robertsmatt97/educational-resonant-demo/KiCAD/Resonant_Edit/Footprints/LLL31MR71C105MA01L.stp

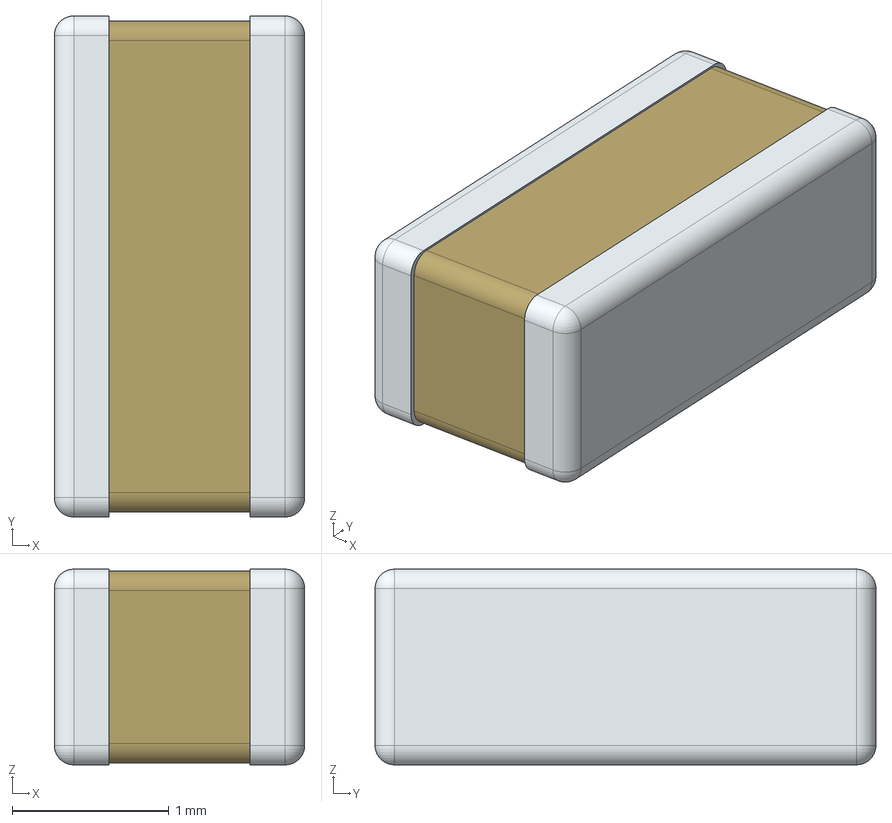
[picture p1: CAD file, 2020-12-04]
KiCAD/Resonant_Edit/Footprints/LLL31MR71C105MA01L.stp
1.60 x 3.20 x 1.25 mm
