robertsmatt97/educational-resonant-demo/KiCAD/Resonant_Edit/Parts/PMEG2010AEH,115.stp

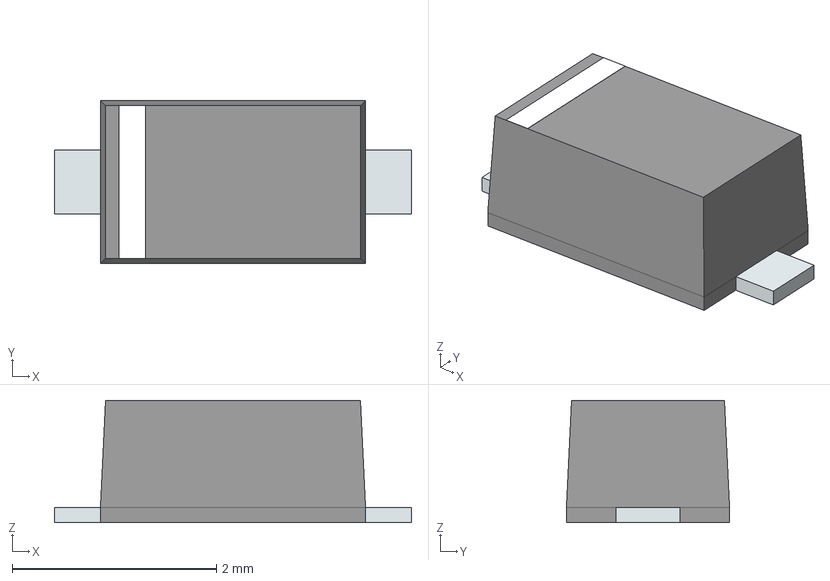
[picture p2: CAD file, 2020-12-04]
KiCAD/Resonant_Edit/Parts/PMEG2010AEH,115.stp
3.50 x 1.60 x 1.20 mm
PinKIdent
PinK
PinA
