robertsmatt97/educational-resonant-demo/KiCAD/Resonant_Edit/Footprints/PTV09A-4020U-B103.stp

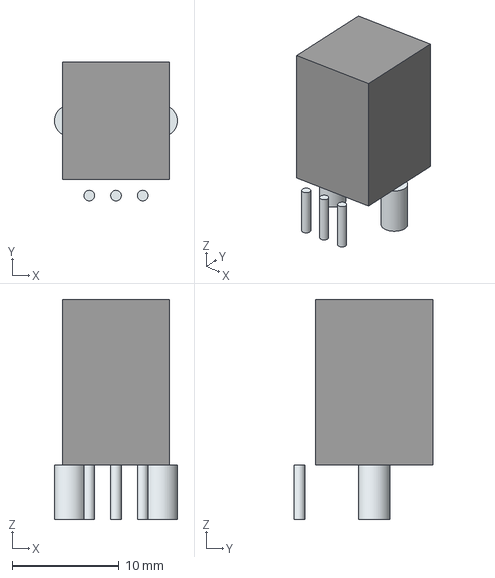
[picture p3: CAD file, 2020-12-04]
KiCAD/Resonant_Edit/Footprints/PTV09A-4020U-B103.stp
11.5 x 13.0 x 20.6 mm
Leads x 5
