robertsmatt97/educational-resonant-demo/KiCAD/Resonant_Edit/Footprints/VSSC8L45-M3_9AT.stp

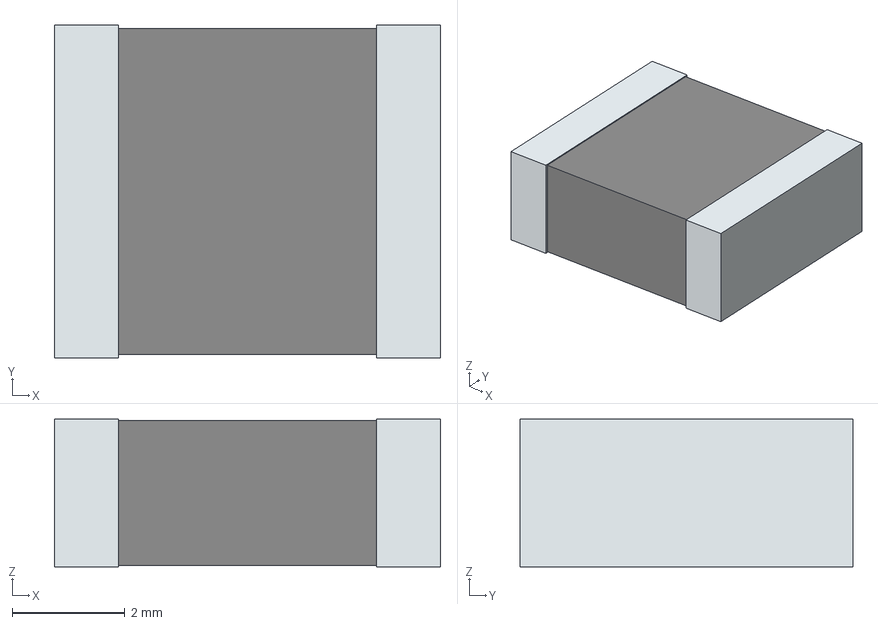
[picture p4: CAD file, 2020-12-04]
KiCAD/Resonant_Edit/Footprints/VSSC8L45-M3_9AT.stp
6.86 x 5.91 x 2.62 mm
term1
term2
