robertsmatt97/educational-resonant-demo/KiCAD/Resonant_Edit/Parts/MBR1H100SFT3G.stp

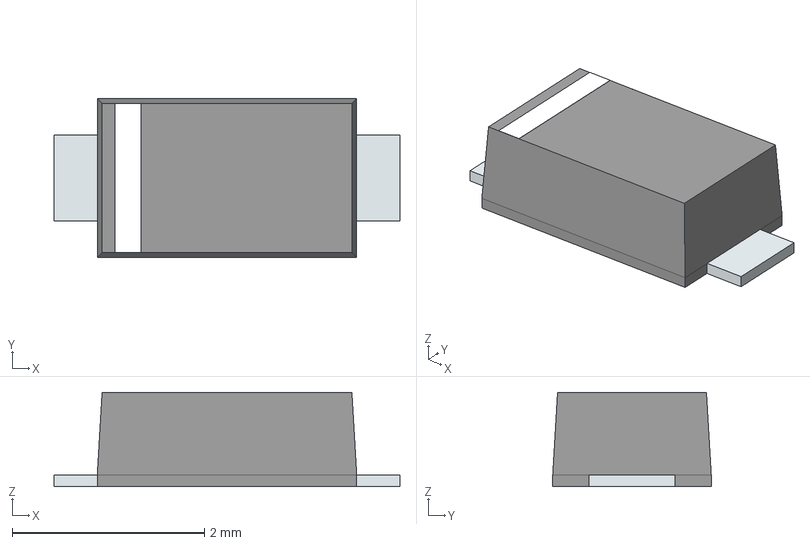
[picture p5: CAD file, 2020-12-04]
KiCAD/Resonant_Edit/Parts/MBR1H100SFT3G.stp
3.60 x 1.65 x 0.98 mm
PinKIdent
PinK
PinA
