robertsmatt97/educational-resonant-demo/KiCAD/Resonant_Edit/Footprints/LM5109BSD_NOPB.stp

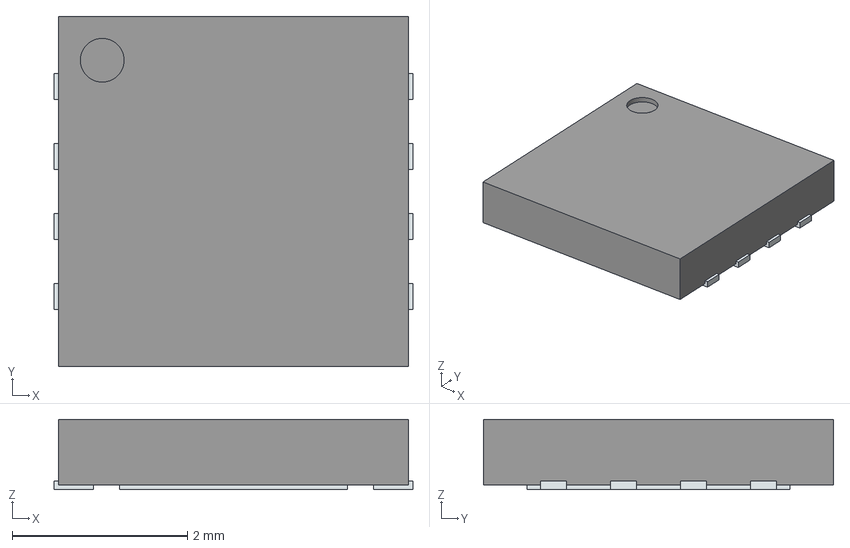
[picture p6: CAD file, 2020-12-04]
KiCAD/Resonant_Edit/Footprints/LM5109BSD_NOPB.stp
4.10 x 4.00 x 0.8 mm
ThermalPin
PinsArrayLR
