robertsmatt97/educational-resonant-demo/KiCAD/Resonant_Edit/Footprints/TLV2632IDR.stp

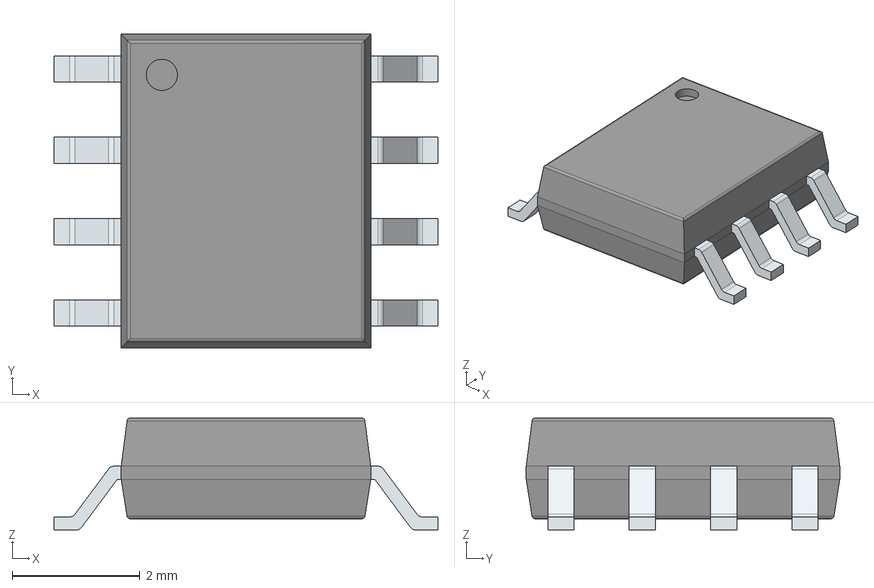
[picture p7: CAD file, 2020-12-04]
KiCAD/Resonant_Edit/Footprints/TLV2632IDR.stp
6.00 x 4.90 x 1.75 mm
PinsArrayLR
