robertsmatt97/educational-resonant-demo/KiCAD/Resonant_Edit/Footprints/PD0120.113NL.stp

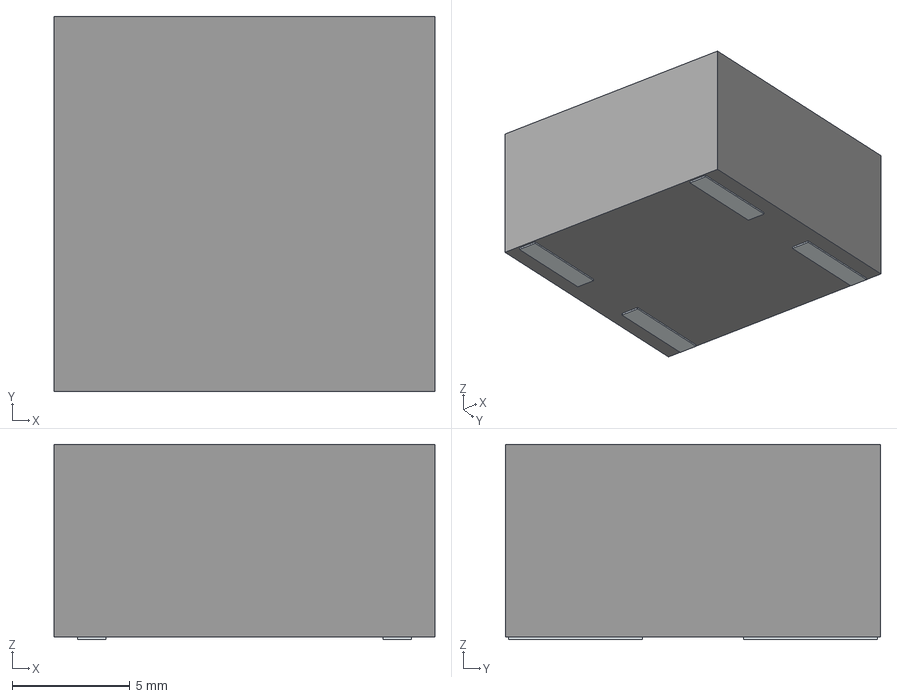
[picture p8: CAD file, 2020-12-04]
KiCAD/Resonant_Edit/Footprints/PD0120.113NL.stp
16.2 x 15.9 x 8.30 mm
Pins
