robertsmatt97/educational-resonant-demo/KiCAD/Resonant_Edit/Footprints/OPA4340UA.stp

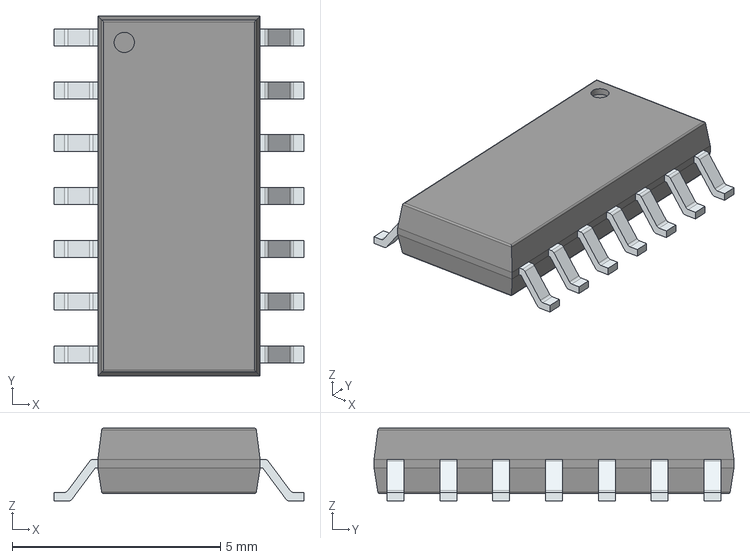
[picture p9: CAD file, 2020-12-04]
KiCAD/Resonant_Edit/Footprints/OPA4340UA.stp
6.00 x 8.65 x 1.75 mm
PinsArrayLR
