robertsmatt97/educational-resonant-demo/LTSpice/Resonant-FHA.asc

CR: cap; {Cr}
LM: ind; {{Ln}*12u}; Ipk=8.2 Rser=0.02 Rpar=3150 Cpar=9.5p
LR: ind; 12µ; Ipk=8.2 Rser=0.02 Rpar=3150 Cpar=9.5p
REQ: res; {{Rload}*0.81057}
RGND: res; 1000k
VFUND: voltage; SINE(0 {{Vdc}*0.45016} {Freq})
Named nets: 0, Vin, Vout, COM
.step param Freq 0 301000 500
.tran 0 1m 0 300n uic
.meas GAIN RMS 0.5*V(Vout)/1.4855 FROM 0.5m TO 1m
.option plotwinsize=0 numdgt=3
.ic v(Vout)={{Vdc}*2}
.param Freq=77750
Configure Parameters here:
Configure Parameters here:
.param Vdc=3.3 Ln=0.67 Cr=211n Rload=40
