robertsmatt97/educational-resonant-demo/LTSpice/Resonant_Full-Bridge.asc

COUT: cap; 5µ
CR: cap; {Cr}
D1: diode; myDiode
D2: diode; myDiode
D3: diode; myDiode
D4: diode; myDiode
LM: ind; {12µ*{Ln}}; Ipk=8.2 Rser=0.02 Rpar=3150 Cpar=9.5p
LMP: ind2; 1
LMS: ind2; 1
LR: ind; 12µ; Ipk=8.2 Rser=0.02 Rpar=3150 Cpar=9.5p
M1: nmos; myNMOS
M2: nmos; myNMOS
RGND: res; 1000k
RL: res; {Rload}
VDC: voltage; {Vdc}
VGH: voltage; PULSE(0 9 0 1n 1n {0.5/{Freq}} {1/{Freq}})
VGL: voltage; PULSE(9 0 0 1n 1n {0.5/{Freq}} {1/{Freq}})
Named nets: 0, COM, Vout, Vin
.step param Freq 0 301000 1000
.tran 0 1m 0 300n uic
.model myDiode D(Ron=0.1n Roff=1Meg Vfwd=0.3 Vrev=30)
.meas GAIN PARAM V(Vout,COM)/V(Vin)
.option plotwinsize=0 numdgt=3
.param Freq=77750
.model myNMOS VDMOS(Vto = 3.3 Ron = 0.001m)
KALL LMP LMS 1
.ic v(Vout)={{Vdc}*2}
Configure Parameters here:
.param Vdc=3.3 Ln=0.67 Cr=211n Rload=40
Configure Parameters here:
