robertsmatt97/educational-resonant-demo/CCS/Resonant_Demo/ADC_Operation.h

/*
 *  ADC_Operation.h
 *
 *  Fall 2020
 *  Matthew Roberts
 *  The University of Texas at Austin
 */

#ifndef ADC_OPERATION_H_
#define ADC_OPERATION_H_
#include <stdint.h>

extern void Adc_A_Init();
extern void Adc_B_Init();
extern void Adc_C_Init();


#endif /* ADC_OPERATION_H_ */
